mgoegel/robotron-esp-vga.pcb/pc1715-esp32vga/images/pc1715-esp32vgar2_pcb.png

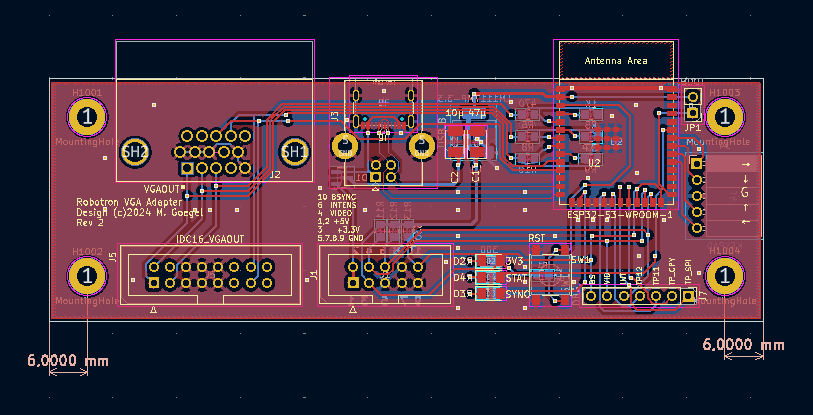
pc1715-esp32vga/images/pc1715-esp32vgar2_pcb.png
